embedrapp/ai-pendant-recorder/include/config.h

#pragma once
#define PENDANT_WIFI_SSID "replace-me"
#define PENDANT_WIFI_PASSWORD "replace-me"
#define PENDANT_API_BASE_URL "https://example.invalid/api"
#define PENDANT_API_TOKEN "replace-me"
#define PENDANT_ASSISTANT_NAME "Second Brain"
#define PENDANT_LANGUAGE "en"
#define PENDANT_PERSONALITY "concise, factual, and helpful"
